schlae/EGAMemory/EGAMemory.kicad_sch

## KiCad design EGAMemory.kicad_sch (2024-01-13)

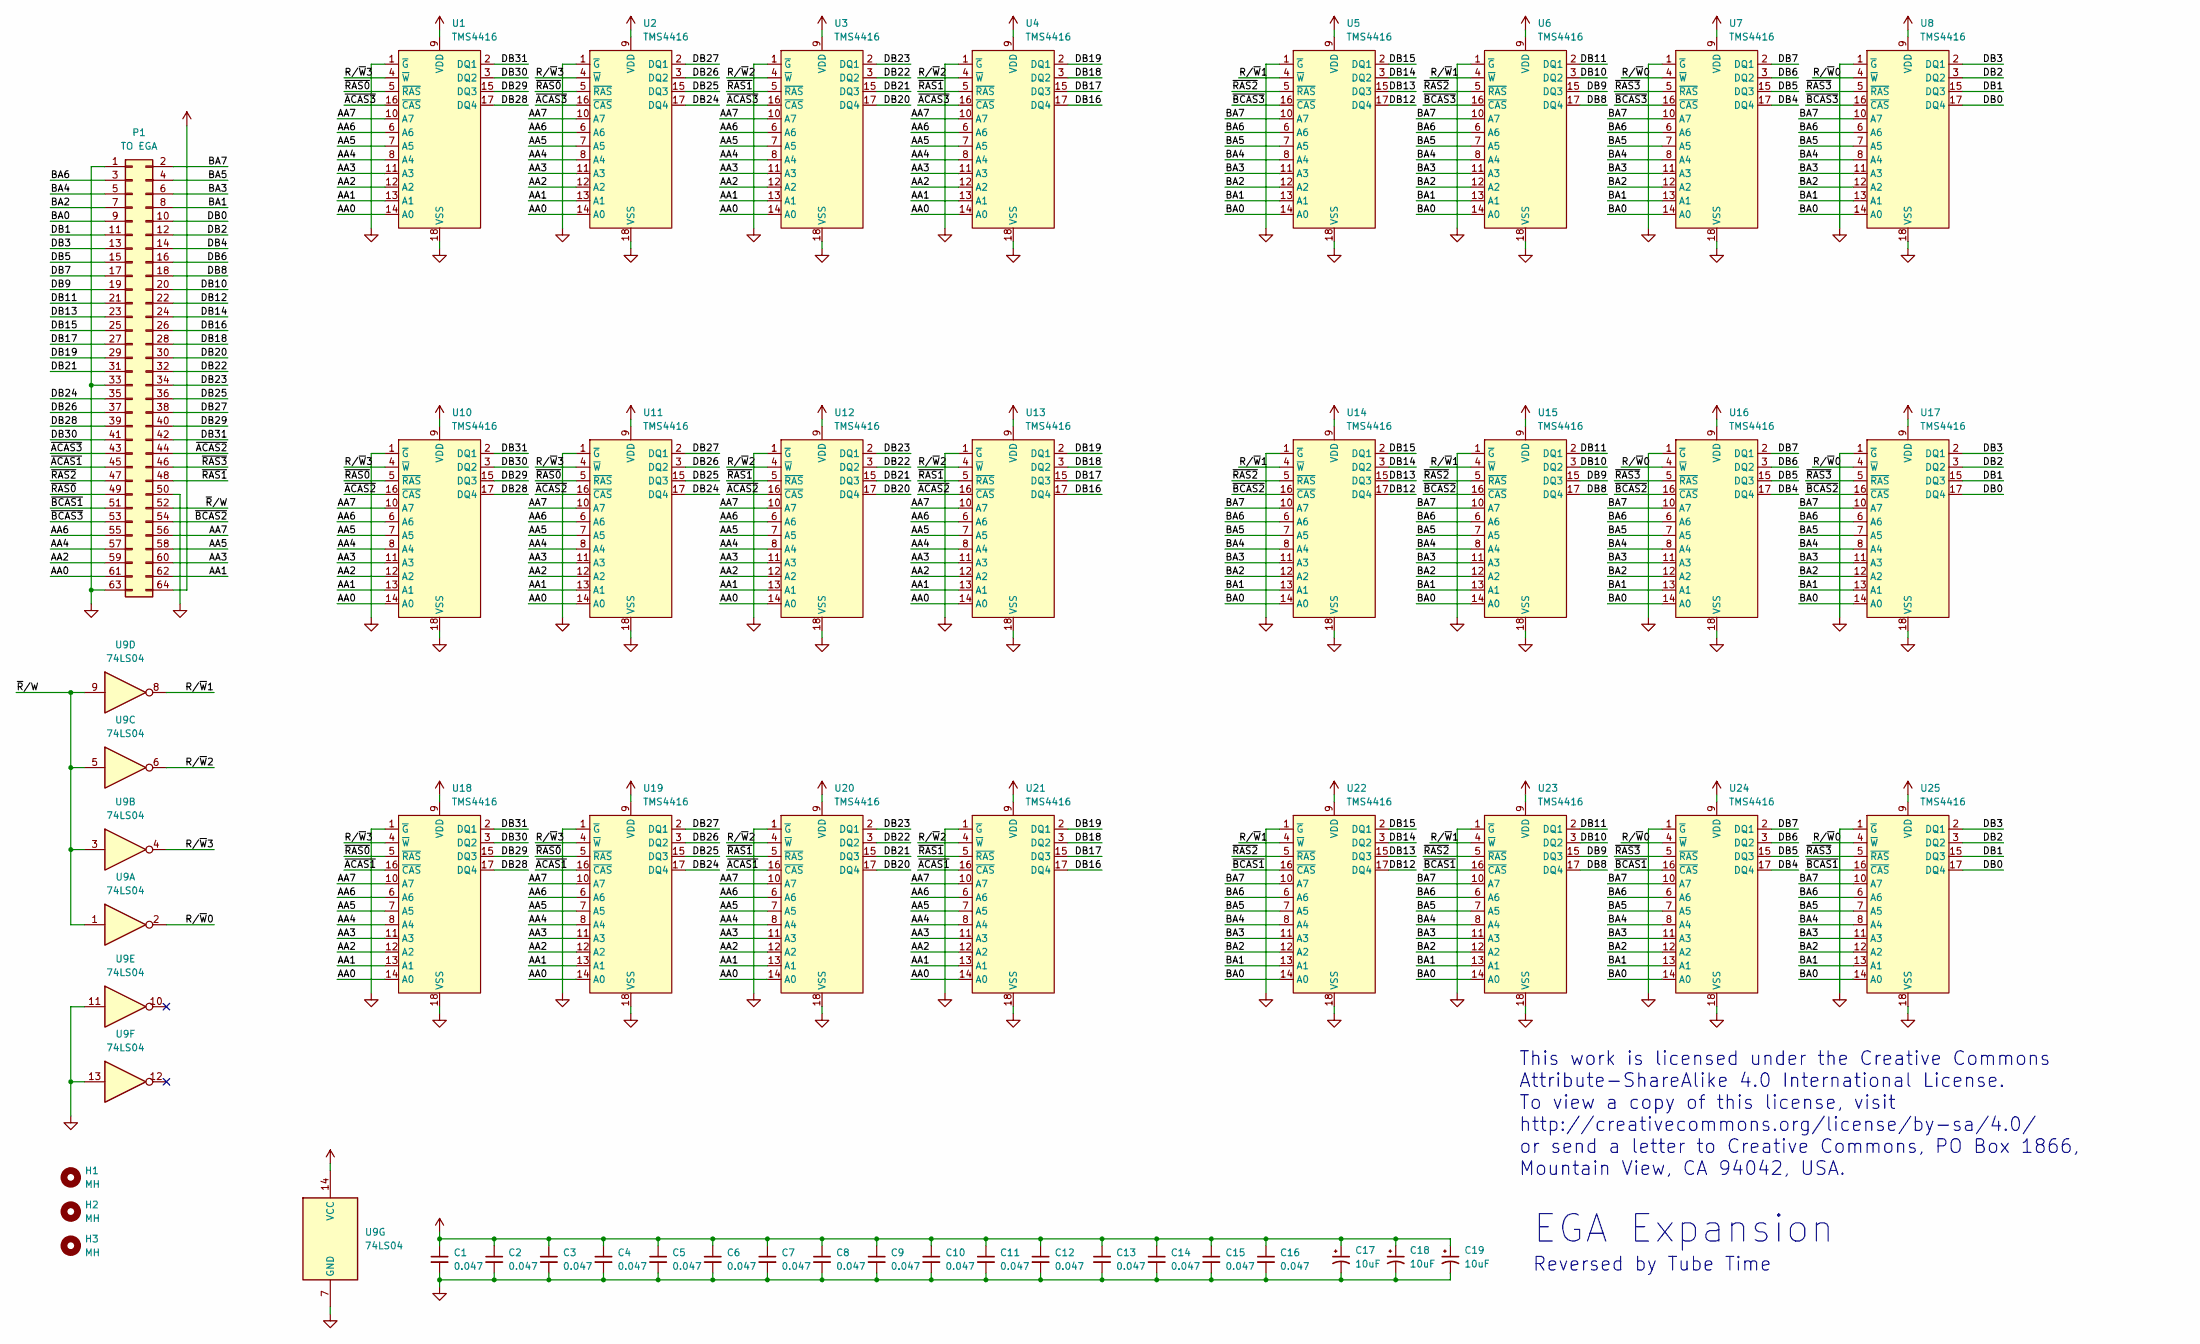
[picture p3: schematic EGAMemory.kicad_sch]

Parts:
C1, C2, C3, C4, C5, C6, C7, C8, C9, C10, C11, C12, C13, C14, C15, C16: 0.047; CAPAC1234; Mouser 594-K473K15X7RF5UH5
C17, C18, C19: 10uF; CAPAP200_ALT; Mouser 80-T398E106M16AT or 74-199D10V10-E
H1, H2: MH; MH185; Mouser 534-8803
H3: MH; MH125
P1: TO EGA; HDR100P32X2; Mouser 571-3-826632-2 or equiv
U1, U2, U3, U4, U5, U6, U7, U8, U10, U11, U12, U13, U14, U15, U16, U17, U18, U19, U20, U21, U22, U23, U24, U25: TMS4416; DIP254P762X635-18
U9: 74LS04; DIP254P762X635-14; Mouser 595-SN74LS04N

Connections:
AA0: P1.61, U1.14 (A0), U2.14 (A0), U3.14 (A0), U4.14 (A0), U10.14 (A0), U11.14 (A0), U12.14 (A0), U13.14 (A0), U18.14 (A0), U19.14 (A0), U20.14 (A0), U21.14 (A0)
AA1: P1.62, U1.13 (A1), U2.13 (A1), U3.13 (A1), U4.13 (A1), U10.13 (A1), U11.13 (A1), U12.13 (A1), U13.13 (A1), U18.13 (A1), U19.13 (A1), U20.13 (A1), U21.13 (A1)
AA2: P1.59, U1.12 (A2), U2.12 (A2), U3.12 (A2), U4.12 (A2), U10.12 (A2), U11.12 (A2), U12.12 (A2), U13.12 (A2), U18.12 (A2), U19.12 (A2), U20.12 (A2), U21.12 (A2)
AA3: P1.60, U1.11 (A3), U2.11 (A3), U3.11 (A3), U4.11 (A3), U10.11 (A3), U11.11 (A3), U12.11 (A3), U13.11 (A3), U18.11 (A3), U19.11 (A3), U20.11 (A3), U21.11 (A3)
AA4: P1.57, U1.8 (A4), U2.8 (A4), U3.8 (A4), U4.8 (A4), U10.8 (A4), U11.8 (A4), U12.8 (A4), U13.8 (A4), U18.8 (A4), U19.8 (A4), U20.8 (A4), U21.8 (A4)
AA5: P1.58, U1.7 (A5), U2.7 (A5), U3.7 (A5), U4.7 (A5), U10.7 (A5), U11.7 (A5), U12.7 (A5), U13.7 (A5), U18.7 (A5), U19.7 (A5), U20.7 (A5), U21.7 (A5)
AA6: P1.55, U1.6 (A6), U2.6 (A6), U3.6 (A6), U4.6 (A6), U10.6 (A6), U11.6 (A6), U12.6 (A6), U13.6 (A6), U18.6 (A6), U19.6 (A6), U20.6 (A6), U21.6 (A6)
AA7: P1.56, U1.10 (A7), U2.10 (A7), U3.10 (A7), U4.10 (A7), U10.10 (A7), U11.10 (A7), U12.10 (A7), U13.10 (A7), U18.10 (A7), U19.10 (A7), U20.10 (A7), U21.10 (A7)
BA0: P1.9, U5.14 (A0), U6.14 (A0), U7.14 (A0), U8.14 (A0), U14.14 (A0), U15.14 (A0), U16.14 (A0), U17.14 (A0), U22.14 (A0), U23.14 (A0), U24.14 (A0), U25.14 (A0)
BA1: P1.8, U5.13 (A1), U6.13 (A1), U7.13 (A1), U8.13 (A1), U14.13 (A1), U15.13 (A1), U16.13 (A1), U17.13 (A1), U22.13 (A1), U23.13 (A1), U24.13 (A1), U25.13 (A1)
BA2: P1.7, U5.12 (A2), U6.12 (A2), U7.12 (A2), U8.12 (A2), U14.12 (A2), U15.12 (A2), U16.12 (A2), U17.12 (A2), U22.12 (A2), U23.12 (A2), U24.12 (A2), U25.12 (A2)
BA3: P1.6, U5.11 (A3), U6.11 (A3), U7.11 (A3), U8.11 (A3), U14.11 (A3), U15.11 (A3), U16.11 (A3), U17.11 (A3), U22.11 (A3), U23.11 (A3), U24.11 (A3), U25.11 (A3)
BA4: P1.5, U5.8 (A4), U6.8 (A4), U7.8 (A4), U8.8 (A4), U14.8 (A4), U15.8 (A4), U16.8 (A4), U17.8 (A4), U22.8 (A4), U23.8 (A4), U24.8 (A4), U25.8 (A4)
BA5: P1.4, U5.7 (A5), U6.7 (A5), U7.7 (A5), U8.7 (A5), U14.7 (A5), U15.7 (A5), U16.7 (A5), U17.7 (A5), U22.7 (A5), U23.7 (A5), U24.7 (A5), U25.7 (A5)
BA6: P1.3, U5.6 (A6), U6.6 (A6), U7.6 (A6), U8.6 (A6), U14.6 (A6), U15.6 (A6), U16.6 (A6), U17.6 (A6), U22.6 (A6), U23.6 (A6), U24.6 (A6), U25.6 (A6)
BA7: P1.2, U5.10 (A7), U6.10 (A7), U7.10 (A7), U8.10 (A7), U14.10 (A7), U15.10 (A7), U16.10 (A7), U17.10 (A7), U22.10 (A7), U23.10 (A7), U24.10 (A7), U25.10 (A7)
DB0: P1.10, U8.17 (DQ4), U17.17 (DQ4), U25.17 (DQ4)
DB1: P1.11, U8.15 (DQ3), U17.15 (DQ3), U25.15 (DQ3)
DB2: P1.12, U8.3 (DQ2), U17.3 (DQ2), U25.3 (DQ2)
DB3: P1.13, U8.2 (DQ1), U17.2 (DQ1), U25.2 (DQ1)
DB4: P1.14, U7.17 (DQ4), U16.17 (DQ4), U24.17 (DQ4)
DB5: P1.15, U7.15 (DQ3), U16.15 (DQ3), U24.15 (DQ3)
DB6: P1.16, U7.3 (DQ2), U16.3 (DQ2), U24.3 (DQ2)
DB7: P1.17, U7.2 (DQ1), U16.2 (DQ1), U24.2 (DQ1)
DB8: P1.18, U6.17 (DQ4), U15.17 (DQ4), U23.17 (DQ4)
DB9: P1.19, U6.15 (DQ3), U15.15 (DQ3), U23.15 (DQ3)
DB10: P1.20, U6.3 (DQ2), U15.3 (DQ2), U23.3 (DQ2)
DB11: P1.21, U6.2 (DQ1), U15.2 (DQ1), U23.2 (DQ1)
DB12: P1.22, U5.17 (DQ4), U14.17 (DQ4), U22.17 (DQ4)
DB13: P1.23, U5.15 (DQ3), U14.15 (DQ3), U22.15 (DQ3)
DB14: P1.24, U5.3 (DQ2), U14.3 (DQ2), U22.3 (DQ2)
DB15: P1.25, U5.2 (DQ1), U14.2 (DQ1), U22.2 (DQ1)
DB16: P1.26, U4.17 (DQ4), U13.17 (DQ4), U21.17 (DQ4)
DB17: P1.27, U4.15 (DQ3), U13.15 (DQ3), U21.15 (DQ3)
DB18: P1.28, U4.3 (DQ2), U13.3 (DQ2), U21.3 (DQ2)
DB19: P1.29, U4.2 (DQ1), U13.2 (DQ1), U21.2 (DQ1)
DB20: P1.30, U3.17 (DQ4), U12.17 (DQ4), U20.17 (DQ4)
DB21: P1.31, U3.15 (DQ3), U12.15 (DQ3), U20.15 (DQ3)
DB22: P1.32, U3.3 (DQ2), U12.3 (DQ2), U20.3 (DQ2)
DB23: P1.34, U3.2 (DQ1), U12.2 (DQ1), U20.2 (DQ1)
DB24: P1.35, U2.17 (DQ4), U11.17 (DQ4), U19.17 (DQ4)
DB25: P1.36, U2.15 (DQ3), U11.15 (DQ3), U19.15 (DQ3)
DB26: P1.37, U2.3 (DQ2), U11.3 (DQ2), U19.3 (DQ2)
DB27: P1.38, U2.2 (DQ1), U11.2 (DQ1), U19.2 (DQ1)
DB28: P1.39, U1.17 (DQ4), U10.17 (DQ4), U18.17 (DQ4)
DB29: P1.40, U1.15 (DQ3), U10.15 (DQ3), U18.15 (DQ3)
DB30: P1.41, U1.3 (DQ2), U10.3 (DQ2), U18.3 (DQ2)
DB31: P1.42, U1.2 (DQ1), U10.2 (DQ1), U18.2 (DQ1)
GND: C1.2, C2.2, C3.2, C4.2, C5.2, C6.2, C7.2, C8.2, C9.2, C10.2, C11.2, C12.2, C13.2, C14.2, C15.2, C16.2, C17.2, C18.2, C19.2, P1.1, P1.33, P1.50, P1.63, U1.1 (~G), U1.18 (VSS), U2.1 (~G), U2.18 (VSS), U3.1 (~G), U3.18 (VSS), U4.1 (~G), U4.18 (VSS), U5.1 (~G), U5.18 (VSS), U6.1 (~G), U6.18 (VSS), U7.1 (~G), U7.18 (VSS), U8.1 (~G), U8.18 (VSS), U9.7 (GND), U9.11, U9.13, U10.1 (~G), U10.18 (VSS), U11.1 (~G), U11.18 (VSS), U12.1 (~G), U12.18 (VSS), U13.1 (~G), U13.18 (VSS), U14.1 (~G), U14.18 (VSS), U15.1 (~G), U15.18 (VSS), U16.1 (~G), U16.18 (VSS), U17.1 (~G), U17.18 (VSS), U18.1 (~G), U18.18 (VSS), U19.1 (~G), U19.18 (VSS), U20.1 (~G), U20.18 (VSS), U21.1 (~G), U21.18 (VSS), U22.1 (~G), U22.18 (VSS), U23.1 (~G), U23.18 (VSS), U24.1 (~G), U24.18 (VSS), U25.1 (~G), U25.18 (VSS)
R/~W0: U7.4 (~W), U8.4 (~W), U9.2, U16.4 (~W), U17.4 (~W), U24.4 (~W), U25.4 (~W)
R/~W1: U5.4 (~W), U6.4 (~W), U9.8, U14.4 (~W), U15.4 (~W), U22.4 (~W), U23.4 (~W)
R/~W2: U3.4 (~W), U4.4 (~W), U9.6, U12.4 (~W), U13.4 (~W), U20.4 (~W), U21.4 (~W)
R/~W3: U1.4 (~W), U2.4 (~W), U9.4, U10.4 (~W), U11.4 (~W), U18.4 (~W), U19.4 (~W)
VDD: C1.1, C2.1, C3.1, C4.1, C5.1, C6.1, C7.1, C8.1, C9.1, C10.1, C11.1, C12.1, C13.1, C14.1, C15.1, C16.1, C17.1, C18.1, C19.1, P1.64, U1.9 (VDD), U2.9 (VDD), U3.9 (VDD), U4.9 (VDD), U5.9 (VDD), U6.9 (VDD), U7.9 (VDD), U8.9 (VDD), U9.14 (VCC), U10.9 (VDD), U11.9 (VDD), U12.9 (VDD), U13.9 (VDD), U14.9 (VDD), U15.9 (VDD), U16.9 (VDD), U17.9 (VDD), U18.9 (VDD), U19.9 (VDD), U20.9 (VDD), U21.9 (VDD), U22.9 (VDD), U23.9 (VDD), U24.9 (VDD), U25.9 (VDD)
~ACAS1: P1.45, U18.16 (~CAS), U19.16 (~CAS), U20.16 (~CAS), U21.16 (~CAS)
~ACAS2: P1.44, U10.16 (~CAS), U11.16 (~CAS), U12.16 (~CAS), U13.16 (~CAS)
~ACAS3: P1.43, U1.16 (~CAS), U2.16 (~CAS), U3.16 (~CAS), U4.16 (~CAS)
~BCAS1: P1.51, U22.16 (~CAS), U23.16 (~CAS), U24.16 (~CAS), U25.16 (~CAS)
~BCAS2: P1.54, U14.16 (~CAS), U15.16 (~CAS), U16.16 (~CAS), U17.16 (~CAS)
~BCAS3: P1.53, U5.16 (~CAS), U6.16 (~CAS), U7.16 (~CAS), U8.16 (~CAS)
~RAS0: P1.49, U1.5 (~RAS), U2.5 (~RAS), U10.5 (~RAS), U11.5 (~RAS), U18.5 (~RAS), U19.5 (~RAS)
~RAS1: P1.48, U3.5 (~RAS), U4.5 (~RAS), U12.5 (~RAS), U13.5 (~RAS), U20.5 (~RAS), U21.5 (~RAS)
~RAS2: P1.47, U5.5 (~RAS), U6.5 (~RAS), U14.5 (~RAS), U15.5 (~RAS), U22.5 (~RAS), U23.5 (~RAS)
~RAS3: P1.46, U7.5 (~RAS), U8.5 (~RAS), U16.5 (~RAS), U17.5 (~RAS), U24.5 (~RAS), U25.5 (~RAS)
~R/W: P1.52, U9.1, U9.3, U9.5, U9.9

Notes on the sheet:
This work is licensed under the Creative Commons Attribute-ShareAlike 4.0 International License. To view a copy of this license, visit http://creativecommons.org/license/by-sa/4.0/ or send a letter to Creative Commons, PO Box 1866, Mountain View, CA 94042, USA.
EGA Expansion
Reversed by Tube Time
